NidasioAlberto/signal-generator/code/src/shared/drivers/spi/SPIDefs.h

/* Copyright (c) 2021 Skyward Experimental Rocketry
 * Author: Alberto Nidasio
 *
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
 * THE SOFTWARE IS PROVIDED "AS IS", WITHOUT WARRANTY OF ANY KIND, EXPRESS OR
 * IMPLIED, INCLUDING BUT NOT LIMITED TO THE WARRANTIES OF MERCHANTABILITY,
 * FITNESS FOR A PARTICULAR PURPOSE AND NONINFRINGEMENT. IN NO EVENT SHALL THE
 * AUTHORS OR COPYRIGHT HOLDERS BE LIABLE FOR ANY CLAIM, DAMAGES OR OTHER
 * LIABILITY, WHETHER IN AN ACTION OF CONTRACT, TORT OR OTHERWISE, ARISING FROM,
 * OUT OF OR IN CONNECTION WITH THE SOFTWARE OR THE USE OR OTHER DEALINGS IN
 * THE SOFTWARE.
 */

#pragma once

#include <interfaces/arch_registers.h>
#include <stdint.h>

/**
 * @brief Driver for STM32 low level SPI peripheral.
 *
 * This driver applies to the whole STM32F4xx family.
 *
 * The serial peripheral interface (SPI) allows half/full-duplex, synchronous,
 * serial communication with external devices. The interface can be configured
 * as the master and in this case it provides the communication clock (SCK) to
 * the external slave device. The peripheral is also capable of reliable
 * communication using CRC checking.
 *
 * SPI main features:
 * - Full-duplex synchronous transfers on three lines
 * - 8- or 16-bit transfer frame format selection
 * - Master or slave operation
 * - 8 master mode baud rate prescaler (f_PCLK/2 max.)
 * - Programmable clock polarity and phase
 * - Programmable data order with MSB-first or LSB-first shifting
 * - Hardware CRC feature for reliable communication
 * - DMA capability
 */
namespace SPI {

enum class Order : uint16_t { MSB_FIRST = 0, LSB_FIRST = SPI_CR1_LSBFIRST };

/**
 * @brief SPI Clock divider.
 *
 * SPI clock frequency will be equal to the SPI peripheral bus clock speed
 * divided by the specified value.
 *
 * Eg: DIV_2 --> spi clock freq = f_PCLK / 2
 */
enum class ClockDivider : uint8_t {
    DIV_2 = 0x00,
    DIV_4 = SPI_CR1_BR_0,
    DIV_8 = SPI_CR1_BR_1,
    DIV_16 = SPI_CR1_BR_1 | SPI_CR1_BR_0,
    DIV_32 = SPI_CR1_BR_2,
    DIV_64 = SPI_CR1_BR_2 | SPI_CR1_BR_0,
    DIV_128 = SPI_CR1_BR_2 | SPI_CR1_BR_1,
    DIV_256 = SPI_CR1_BR
};

enum class Mode : uint8_t {
    ///< CPOL = 0, CPHA = 0 -> Clock low when idle, sample on first edge
    MODE_0 = 0,
    ///< CPOL = 0, CPHA = 1 -> Clock low when idle, sample on second edge
    MODE_1 = SPI_CR1_CPHA,
    ///< CPOL = 1, CPHA = 0 -> Clock high when idle, sample on first edge
    MODE_2 = SPI_CR1_CPOL,
    ///< CPOL = 1, CPHA = 1 -> Clock high when idle, sample on second edge
    MODE_3 = SPI_CR1_CPOL | SPI_CR1_CPHA
};

enum class WriteBit {
    NORMAL,    ///< Normal write bit settings (0 for write, 1 for reads)
    INVERTED,  ///< Inverted write bit settings (1 for write, 0 for reads)
    DISABLED,  ///< Do not set write bit in any way
};

}  // namespace SPI
