NidasioAlberto/signal-generator/code/src/shared/drivers/ADC/ADC.cpp

/* Copyright (c) 2023 Skyward Experimental Rocketry
 * Author: Alberto Nidasio
 *
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
 * THE SOFTWARE IS PROVIDED "AS IS", WITHOUT WARRANTY OF ANY KIND, EXPRESS OR
 * IMPLIED, INCLUDING BUT NOT LIMITED TO THE WARRANTIES OF MERCHANTABILITY,
 * FITNESS FOR A PARTICULAR PURPOSE AND NONINFRINGEMENT. IN NO EVENT SHALL THE
 * AUTHORS OR COPYRIGHT HOLDERS BE LIABLE FOR ANY CLAIM, DAMAGES OR OTHER
 * LIABILITY, WHETHER IN AN ACTION OF CONTRACT, TORT OR OTHERWISE, ARISING FROM,
 * OUT OF OR IN CONNECTION WITH THE SOFTWARE OR THE USE OR OTHER DEALINGS IN
 * THE SOFTWARE.
 */

#include "ADC.h"

#include <utils/ClockUtils.h>

static constexpr int ADC_RESOLUTION = 4095;

#if defined(STM32F407xx) || defined(STM32F429xx)
#define CAL_PT1_VALUE ((uint16_t volatile *)((uint32_t)0x1FFF7A2C))
#define CAL_PT2_VALUE ((uint16_t volatile *)((uint32_t)0x1FFF7A2E))
static const float CAL_PT1_TEMP = 30;
static const float CAL_PT2_TEMP = 110;
static const float CAL_V_DDA = 3.3f;
#elif defined(STM32F767xx) || defined(STM32F769xx)
#define CAL_PT1_VALUE ((uint16_t volatile *)((uint32_t)0x1FF0F44C))
#define CAL_PT2_VALUE ((uint16_t volatile *)((uint32_t)0x1FF0F44E))
static const float CAL_PT1_TEMP = 30;
static const float CAL_PT2_TEMP = 110;
static const float CAL_V_DDA = 3.3f;
#else
#warning The current targets does not have a calibrated temperature sensor or is not currently supported by this driver
#endif

#if defined(STM32F407xx) || defined(STM32F205xx)
static const ADCDriver::Channel TEMP_CH = ADCDriver::Channel::CH16;
static const ADCDriver::Channel VBAT_CH = ADCDriver::Channel::CH18;
static const float VBAT_DIV = 2.0f;
#elif defined(STM32F429xx) || defined(STM32F767xx) || defined(STM32F769xx)
static const ADCDriver::Channel TEMP_CH = ADCDriver::Channel::CH18;
static const ADCDriver::Channel VBAT_CH = ADCDriver::Channel::CH18;
static const float VBAT_DIV = 4.0f;
#endif

// Error the user if the current target is missing the V_DDA_VOLTAGE macro
// If it is missing you need to define it, preferably in the board_settings.h
// file in miosix. Check your board schematic to find the voltage value.
#ifndef V_DDA_VOLTAGE
#error Missing V_DDA_VOLTAGE definition for current target
#endif

ADCDriver::ADCDriver(ADC_TypeDef *adc) : adc(adc) {
#ifndef INTERNAL_ADC_WITHOUT_CALIBRATION
    loadCalibrationValues();
#endif

    resetRegisters();
    ClockUtils::enablePeripheralClock(adc);

    // Set the clock divider for the analog circuitry to the highest value (/8).
    // Currently there is no need to speed up ADC reading. For this reason we
    // use the safest setting.
    // If it will need to be changed you need to check the datasheet for the
    // maximum frequency the analog circuitry supports and compare it with the
    // parent clock (APB2). Also you need to take into account the sampling time
    // for the temperature sensor.
    ADC->CCR |= ADC_CCR_ADCPRE_1 | ADC_CCR_ADCPRE_0;
}

ADCDriver::~ADCDriver() {
    resetRegisters();
    ClockUtils::disablePeripheralClock(adc);
}

void ADCDriver::enable() { adc->CR2 |= ADC_CR2_ADON; }

void ADCDriver::disable() { adc->CR2 &= ~ADC_CR2_ADON; }

void ADCDriver::sample() {
    for (int i = 0; i < static_cast<uint8_t>(Channel::CH16); i++) {
        if (channelsEnabled[i]) {
            voltages[i] = readChannel(static_cast<Channel>(i));
            voltages[i] =
                voltages[i] *
                V_DDA_VOLTAGE  // cppcheck-suppress ConfigurationNotChecked
                / ADC_RESOLUTION;
        }
    }

    // Quirk: the temperature and Vbat sensors are enabled and then disabled. If
    // left enabled they somehow disrupt other channels measurements. I did not
    // find description of this behaviour anywhere but observed it during
    // testing. Also the temperature sensors has a startup time of 10us. 12us is
    // used because during test 10us were not enough.
    // The startup time is the same for all supported micros.

    if (tempEnabled) {
        ADC->CCR |= ADC_CCR_TSVREFE;
        miosix::delayUs(12);  // Temperature sensor startup time
        auto temperatureRawValue = readChannel(static_cast<Channel>(TEMP_CH));
        ADC->CCR &= ~ADC_CCR_TSVREFE;

        // Conversion
        if (temperatureRawValue != 0) {
            temperature =
                temperatureRawValue *
                V_DDA_VOLTAGE  // cppcheck-suppress ConfigurationNotChecked
                / ADC_RESOLUTION;

#ifdef INTERNAL_ADC_WITHOUT_CALIBRATION
            // Default conversion
            temperature = ((temperature - 0.76) / 0.0025) + 25;
#else
            // Factory calibration
            temperature = temperature - calPt1Voltage;
            temperature /= calSlope;
            temperature += CAL_PT1_TEMP;
#endif
        } else {
            temperature = 0;
        }
    }

    if (vbatEnabled) {
        ADC->CCR |= ADC_CCR_VBATE;
        auto vbatVoltageRawValue = readChannel(static_cast<Channel>(VBAT_CH));
        ADC->CCR &= ~ADC_CCR_VBATE;

        vBat = vbatVoltageRawValue *
               V_DDA_VOLTAGE  // cppcheck-suppress ConfigurationNotChecked
               / ADC_RESOLUTION * VBAT_DIV;
    }
}

void ADCDriver::enableChannel(Channel channel, SampleTime sampleTime) {
    channelsEnabled[static_cast<uint8_t>(channel)] = true;

    setChannelSampleTime(channel, sampleTime);
}

void ADCDriver::disableChannel(Channel channel) {
    channelsEnabled[static_cast<uint8_t>(channel)] = false;
}

void ADCDriver::enableRegularSequenceTrigger(RegularTriggerSource triggerSource,
                                             TriggerPolarity triggerPolarity) {
    adc->CR2 |= static_cast<uint32_t>(triggerSource) |
                static_cast<uint32_t>(triggerPolarity);
}

void ADCDriver::disableRegularSequenceTrigger() {
    adc->CR2 &= ~(ADC_CR2_EXTEN | ADC_CR2_EXTSEL);
}

void ADCDriver::enableTemperature(SampleTime sampleTime) {
    tempEnabled = true;
    enableChannel(TEMP_CH, sampleTime);
}

void ADCDriver::disableTemperature() {
    tempEnabled = false;
    if (!vbatEnabled || TEMP_CH != VBAT_CH)
        disableChannel(TEMP_CH);
}

void ADCDriver::enableVbat(SampleTime sampleTime) {
    vbatEnabled = true;
    enableChannel(VBAT_CH, sampleTime);
}

void ADCDriver::disableVbat() {
    vbatEnabled = false;
    if (!tempEnabled || TEMP_CH != VBAT_CH)
        disableChannel(VBAT_CH);
}

float ADCDriver::getVoltage(Channel channel) {
    return voltages[static_cast<uint8_t>(channel)];
}

float ADCDriver::getTemperature() { return temperature; }

float ADCDriver::getVbatVoltage() { return vBat; }

void ADCDriver::loadEnabledChannelsInRegularSequence() {
    int position = 0;
    for (int i = 0; i < static_cast<uint8_t>(Channel::CH16); i++) {
        if (channelsEnabled[i]) {
            addRegularChannel(static_cast<Channel>(i), position);
            position++;
        }
    }

    // Update the regular channels number
    adc->SQR1 &= ~ADC_SQR1_L;
    adc->SQR1 |= (position - 1) << ADC_SQR1_L_Pos;
}
void ADCDriver::startRegularSequence() { adc->CR2 |= ADC_CR2_SWSTART; }

void ADCDriver::enableDMA(bool dds) {
    // Rewrite the DMA bit in ADC CR2 to ensure a proper restart
    adc->CR2 &= ~(ADC_CR2_DMA | ADC_CR2_DDS);
    adc->CR2 |= ADC_CR2_DMA | (dds ? ADC_CR2_DDS : 0);
}

void ADCDriver::disableDMA() { adc->CR2 &= ~(ADC_CR2_DMA | ADC_CR2_DDS); }

bool ADCDriver::getOverrunFlag() { return (adc->SR & ADC_SR_OVR) != 0; }

void ADCDriver::clearOverrunFlag() { adc->SR &= ~ADC_SR_OVR; }

inline void ADCDriver::resetRegisters() {
    // Reset the ADC configuration
    adc->CR1 = 0;
    adc->CR2 = 0;
    adc->SMPR1 = 0;
    adc->SMPR2 = 0;
    adc->JOFR1 = 0;
    adc->JOFR2 = 0;
    adc->JOFR3 = 0;
    adc->JOFR4 = 0;
    adc->HTR = 0;
    adc->LTR = 0;
    adc->SQR1 = 0;
    adc->SQR2 = 0;
    adc->SQR3 = 0;
    adc->JSQR = 0;
}

inline void ADCDriver::setChannelSampleTime(Channel channel,
                                            SampleTime sampleTime) {
    uint8_t chNo = static_cast<uint8_t>(channel);

    if (chNo <= 9) {
        adc->SMPR2 &= ~(0x7 << (chNo * 3));
        adc->SMPR2 |= static_cast<uint32_t>(sampleTime) << (chNo * 3);
    } else {
        adc->SMPR1 &= ~(0x7 << ((chNo - 10) * 3));
        adc->SMPR1 |= static_cast<uint32_t>(sampleTime) << ((chNo - 10) * 3);
    }
}

uint16_t ADCDriver::readChannel(Channel channel) {
    // Reset the number of active regular channels
    adc->SQR1 &= ~ADC_SQR1_L;

    // The driver performs multiple regular sequence conversions to keep the
    // code simple

    // Select channel
    adc->SQR3 = static_cast<uint8_t>(channel);

    // Start conversion
    startRegularSequence();

    while (!(adc->SR & ADC_SR_EOC))
        ;

    return static_cast<uint16_t>(adc->DR);
}

bool ADCDriver::addRegularChannel(Channel channel, uint8_t position) {
    // Check the position
    if (position >= 16) {
        return false;
    }

    // Add the channel to the sequence
    volatile uint32_t *sqrPtr;
    switch (position / 6) {
        case 1:
            sqrPtr = &(adc->SQR2);
            break;
        case 2:
            sqrPtr = &(adc->SQR1);
            break;
        default:
            sqrPtr = &(adc->SQR3);
    }
    *sqrPtr &= ~(ADC_SQR3_SQ1 << ((position % 6) * 5));
    *sqrPtr |= static_cast<int>(channel) << ((position % 6) * 5);

    return true;
}

#ifndef INTERNAL_ADC_WITHOUT_CALIBRATION
void ADCDriver::loadCalibrationValues() {
    calPt1Voltage = static_cast<float>(*CAL_PT1_VALUE);
    calPt1Voltage *= CAL_V_DDA / ADC_RESOLUTION;

    calPt2Voltage = static_cast<float>(*CAL_PT2_VALUE);
    calPt2Voltage *= CAL_V_DDA / ADC_RESOLUTION;

    calSlope = calPt1Voltage - calPt2Voltage;
    calSlope /= CAL_PT2_TEMP - CAL_PT1_TEMP;
}
#endif
